alecangus/ArduinoPuzzleBox/images/DSC_0131.JPG

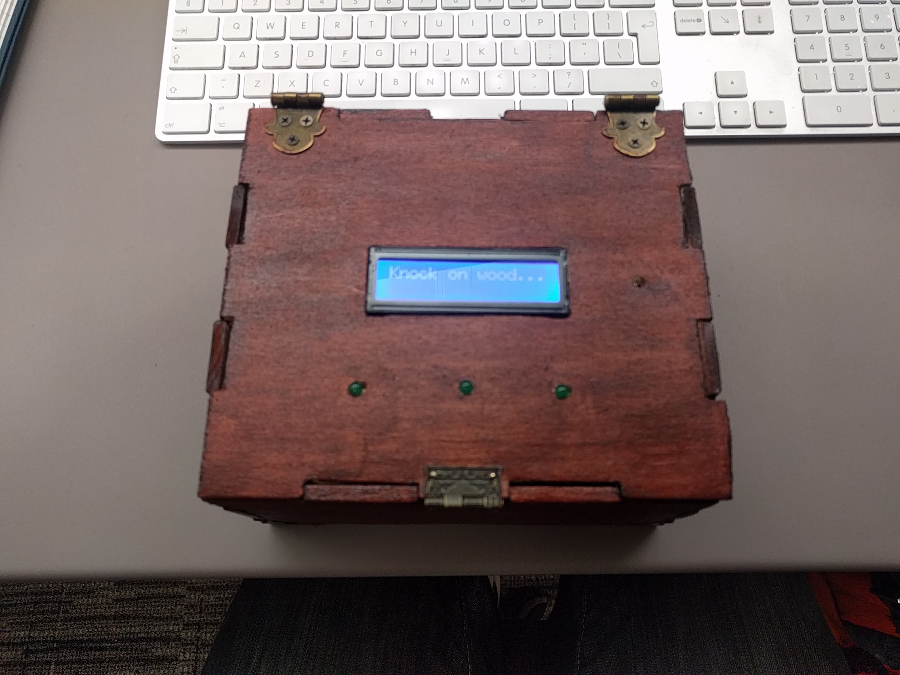
images/DSC_0131.JPG
