alecangus/ArduinoPuzzleBox/images/DSC_0160.JPG

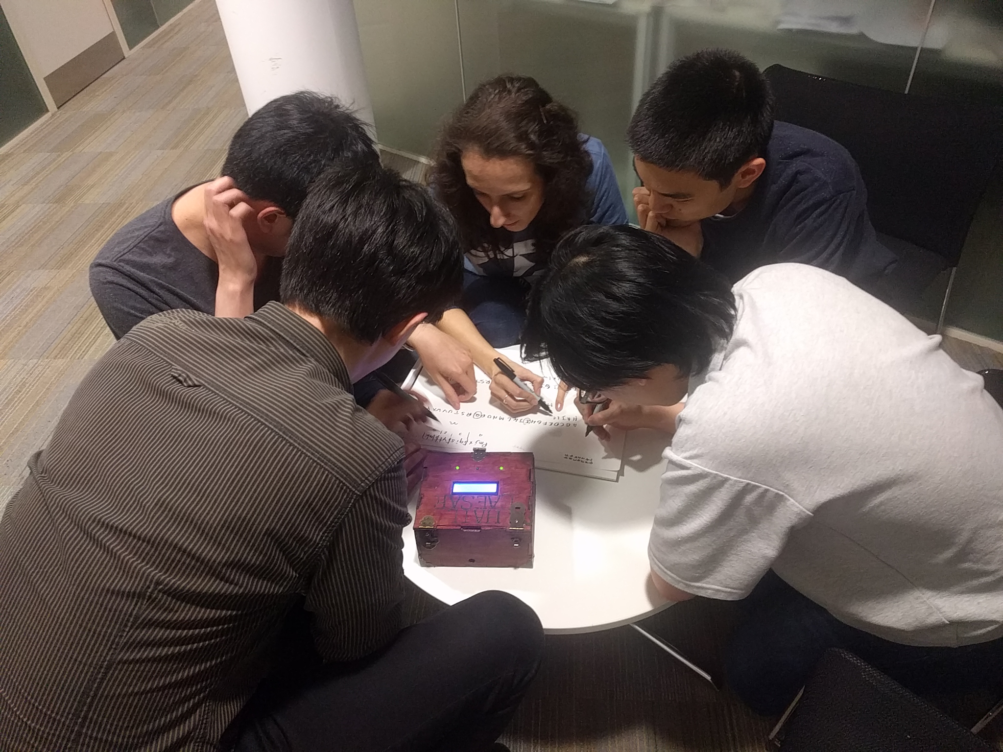
images/DSC_0160.JPG
